Sillybutts/Cynthia/STLs/Black/PlungerRod_Thinner (for tighter springs like k26).stl

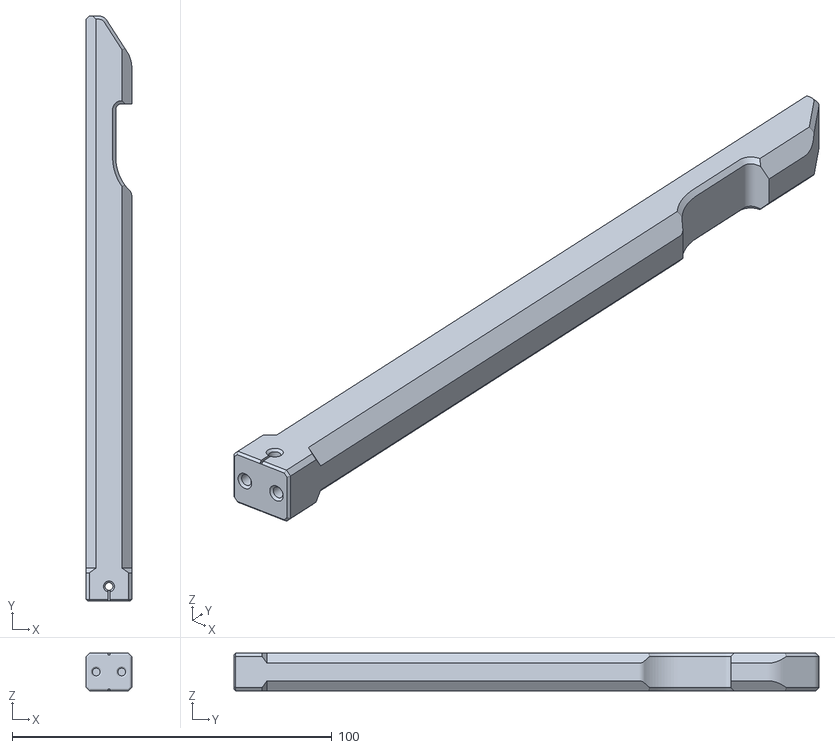
[picture p39: CAD file, 2023-04-10]
STLs/Black/PlungerRod_Thinner (for tighter springs like k26).stl
14.3 x 182.9 x 11.7
