Sillybutts/Cynthia/STLs/Green/Left Handed/MagwellBack_LH_Locked.stl

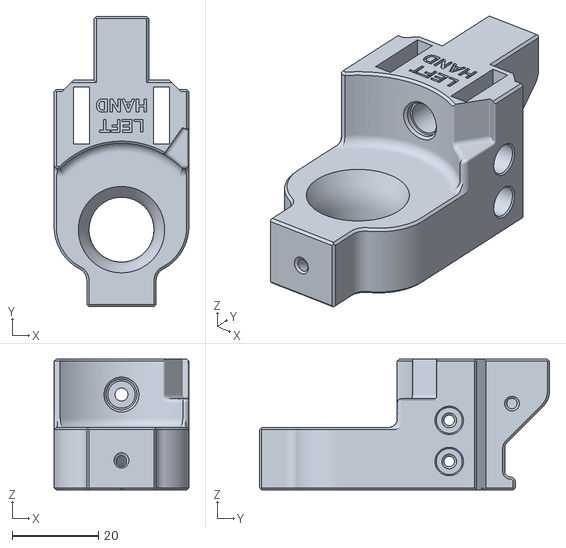
[picture p40: CAD file, 2023-03-23]
STLs/Green/Left Handed/MagwellBack_LH_Locked.stl
31.2 x 67.2 x 30.3
