Sillybutts/Cynthia/STLs/Orange/Trigger_SillyStyle.stl

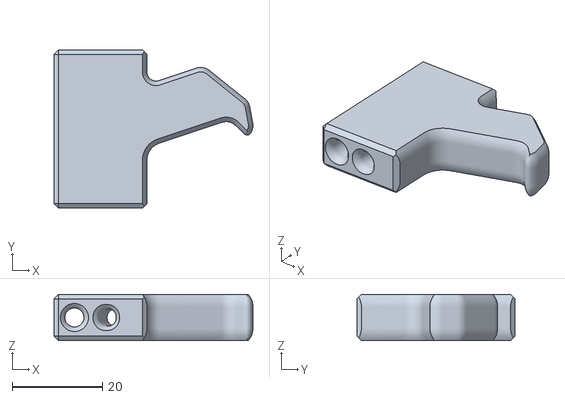
[picture p41: CAD file, 2023-03-23]
STLs/Orange/Trigger_SillyStyle.stl
44.0 x 35.0 x 10.2
