Sillybutts/Cynthia/STLs/Alternate and Experimental/Alternate Mag Release and Trigger Guard/TriggerGuard_LONGERFORALTERNATEMAGRELEASE.stl

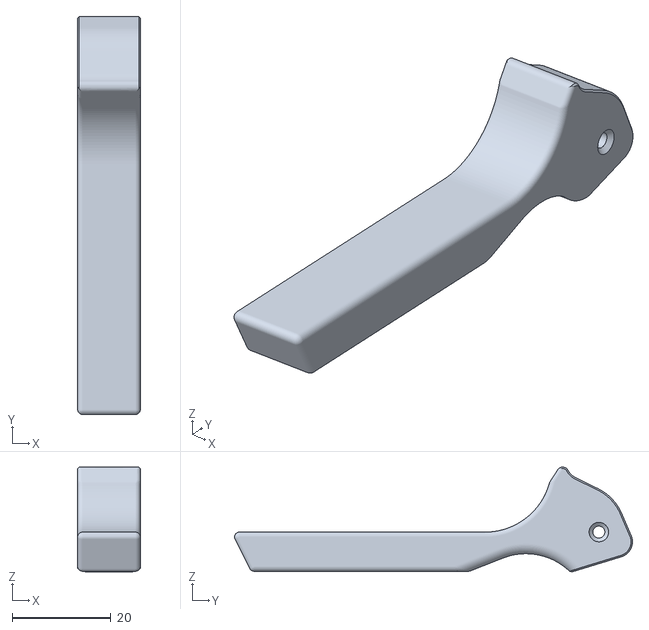
[picture p42: CAD file, 2023-03-24]
STLs/Alternate and Experimental/Alternate Mag Release and Trigger Guard/TriggerGuard_LONGERFORALTERNATEMAGRELEASE.stl
12.7 x 80.5 x 21.2
