Sillybutts/Cynthia/STLs/Alternate and Experimental/Shortened front (needs 5.5inch threaded rod)/SHORTENED_TopRail_SplitA.stl

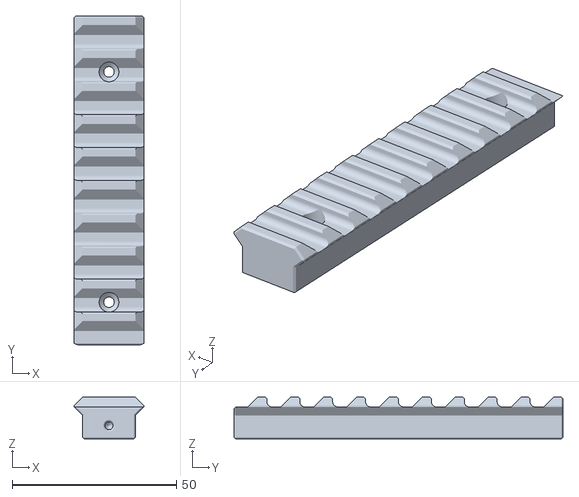
[picture p43: CAD file, 2023-04-16]
STLs/Alternate and Experimental/Shortened front (needs 5.5inch threaded rod)/SHORTENED_TopRail_SplitA.stl
21.2 x 100.1 x 12.7
