Sillybutts/Cynthia/STLs/Alternate and Experimental/Slim front end/SLIM_Muzzle_WithBottomRail.stl

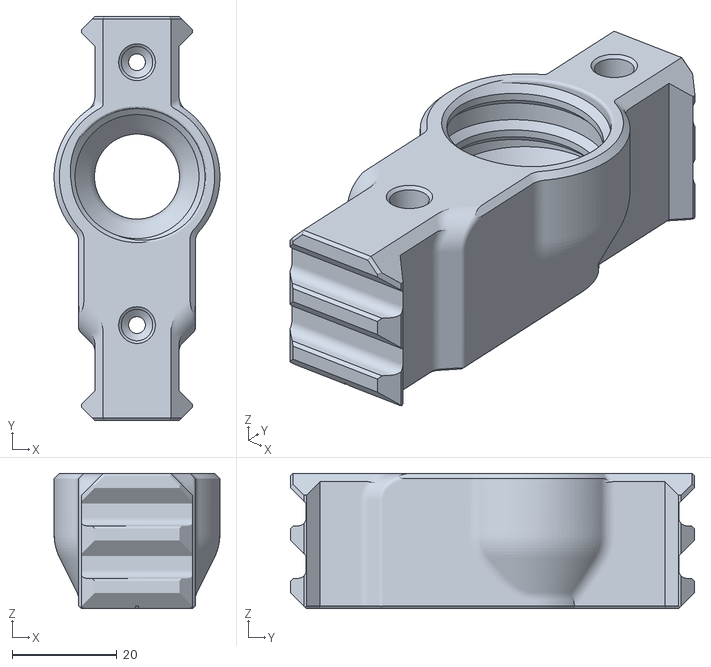
[picture p44: CAD file, 2023-03-23]
STLs/Alternate and Experimental/Slim front end/SLIM_Muzzle_WithBottomRail.stl
31.6 x 77.0 x 25.8
