Sillybutts/Cynthia/STLs/Alternate and Experimental/Split PTcover for smaller printers/SPLIT_PTcoverFront_Logo.stl

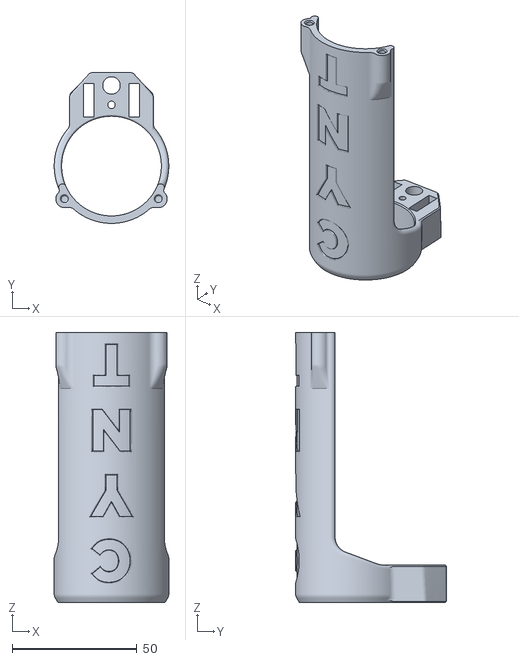
[picture p45: CAD file, 2023-06-04]
STLs/Alternate and Experimental/Split PTcover for smaller printers/SPLIT_PTcoverFront_Logo.stl
46.0 x 60.5 x 108.3
