Sillybutts/Cynthia/STLs/Alternate and Experimental/Stubby front end/DartGuide_Alternate.stl

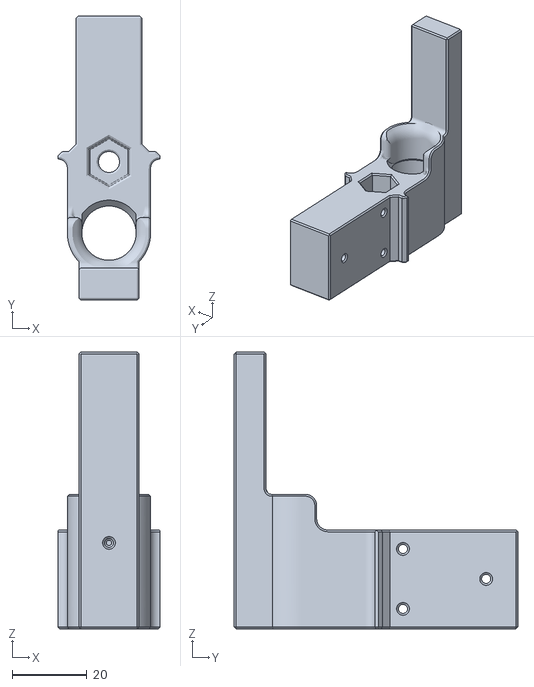
[picture p46: CAD file, 2023-03-23]
STLs/Alternate and Experimental/Stubby front end/DartGuide_Alternate.stl
27.2 x 75.7 x 74.0
