Sillybutts/Cynthia/STLs/Black/Stock_SlingPoints.stl

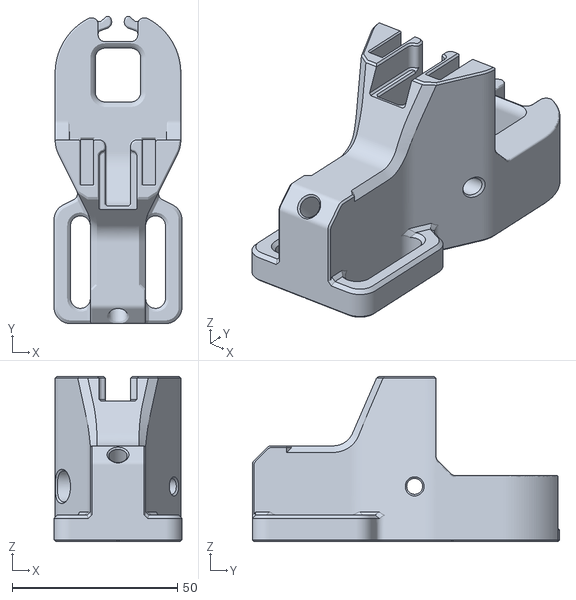
[picture p47: CAD file, 2023-03-23]
STLs/Black/Stock_SlingPoints.stl
38.8 x 93.1 x 50.0
