Sillybutts/Cynthia/STLs/Green/PTcover_Logo.stl

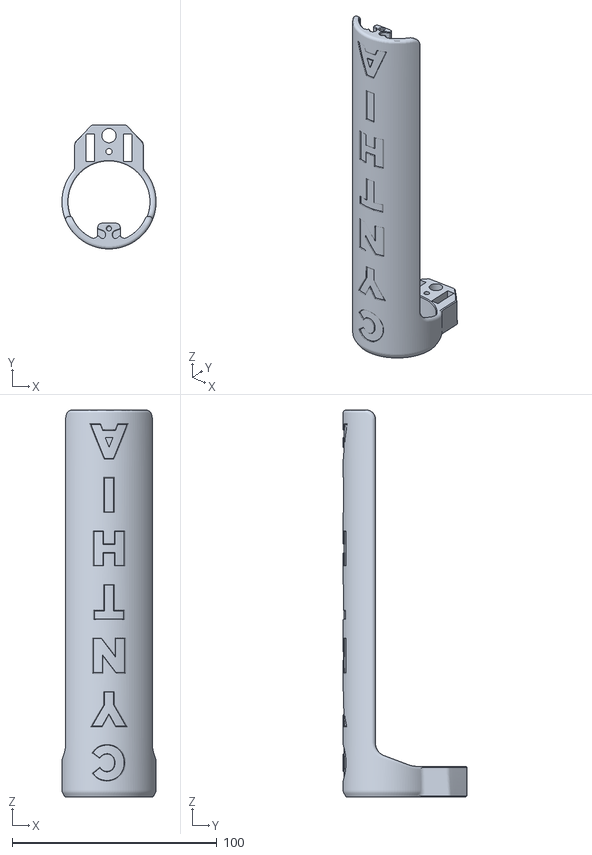
[picture p48: CAD file, 2023-03-27]
STLs/Green/PTcover_Logo.stl
46.0 x 60.5 x 189.1
