Sillybutts/Cynthia/STLs/Orange/Muzzle_WithBottomRail.stl

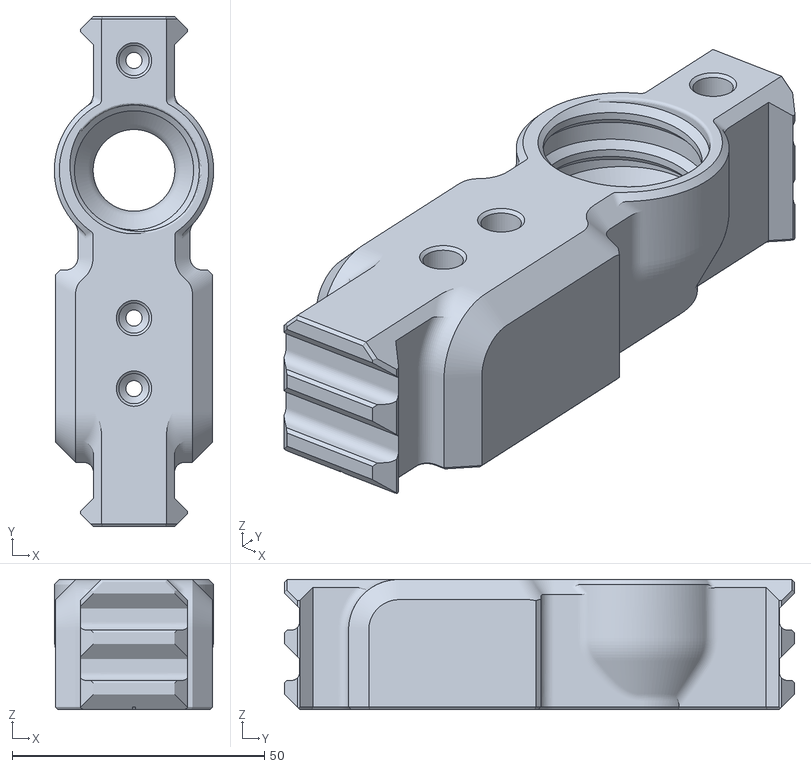
[picture p49: CAD file, 2023-03-23]
STLs/Orange/Muzzle_WithBottomRail.stl
31.6 x 101.2 x 25.8
