Sillybutts/Cynthia/STLs/Alternate and Experimental/MegaXL Spigot SCAR/BarrelCap.stl

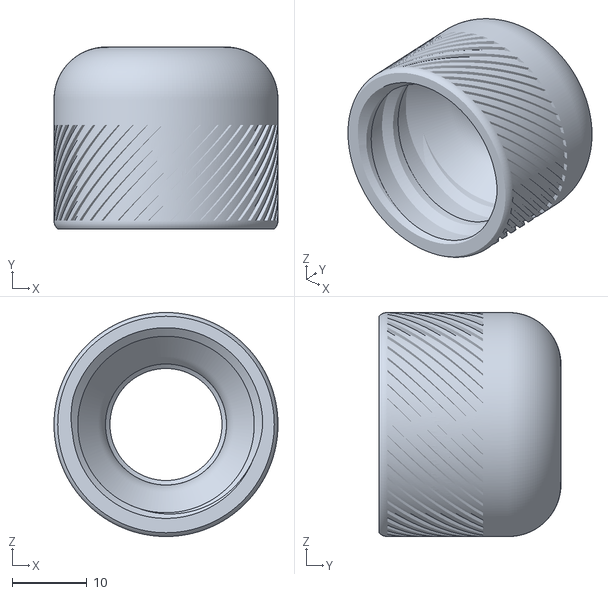
[picture p50: CAD file, 2023-03-23]
STLs/Alternate and Experimental/MegaXL Spigot SCAR/BarrelCap.stl
30.0 x 24.4 x 30.0
