Sillybutts/Cynthia/STLs/Alternate and Experimental/Shortened front (needs 5.5inch threaded rod)/SHORTENED_BottomRail.stl

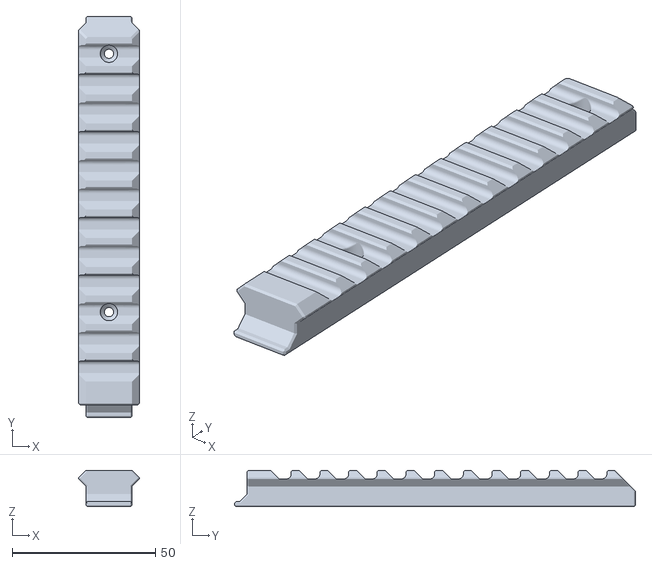
[picture p51: CAD file, 2023-04-16]
STLs/Alternate and Experimental/Shortened front (needs 5.5inch threaded rod)/SHORTENED_BottomRail.stl
21.2 x 139.8 x 12.7
