Sillybutts/Cynthia/STLs/Alternate and Experimental/Stubby front end/MuzzleNut.stl

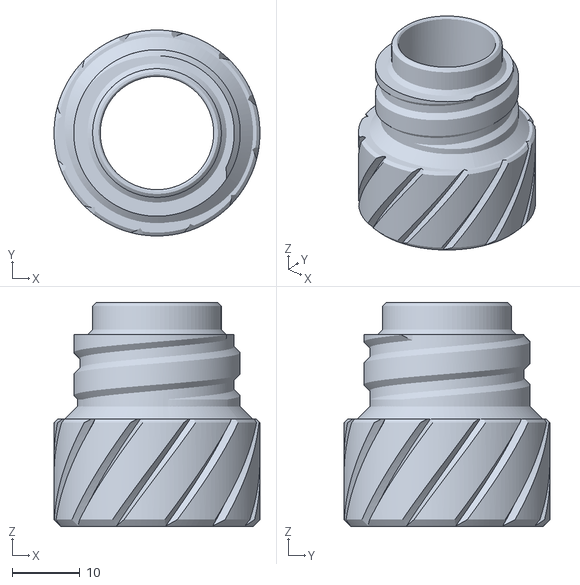
[picture p53: CAD file, 2023-03-23]
STLs/Alternate and Experimental/Stubby front end/MuzzleNut.stl
30.5 x 30.5 x 33.1
