Sillybutts/Cynthia/STLs/Alternate and Experimental/Triggers for optional 10-32 Heat Set Insert/HEATSET_Trigger_ChanceStyle.stl

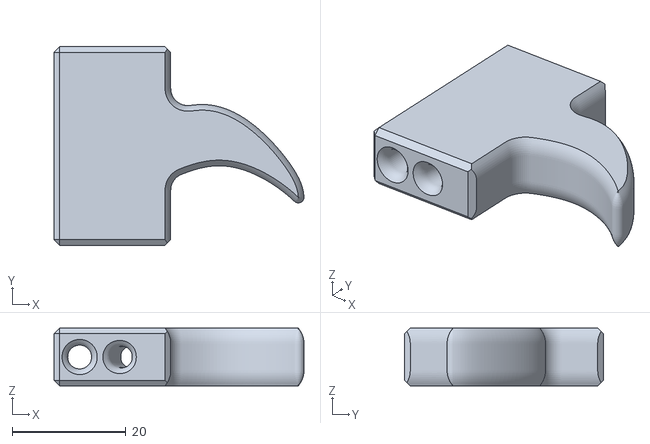
[picture p54: CAD file, 2023-03-23]
STLs/Alternate and Experimental/Triggers for optional 10-32 Heat Set Insert/HEATSET_Trigger_ChanceStyle.stl
44.0 x 35.0 x 10.2
