Sillybutts/Cynthia/STLs/Black/GripBody_NoShoe.stl

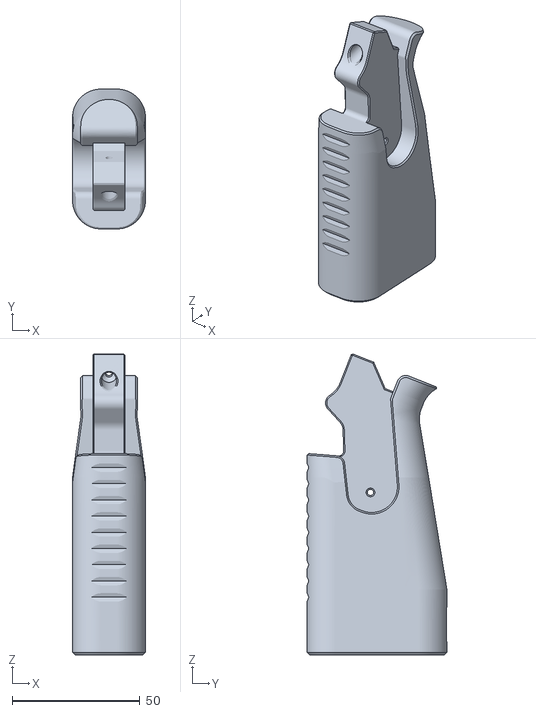
[picture p55: CAD file, 2023-03-23]
STLs/Black/GripBody_NoShoe.stl
28.6 x 54.8 x 117.9
