Sillybutts/Cynthia/STLs/Orange/Catch.stl

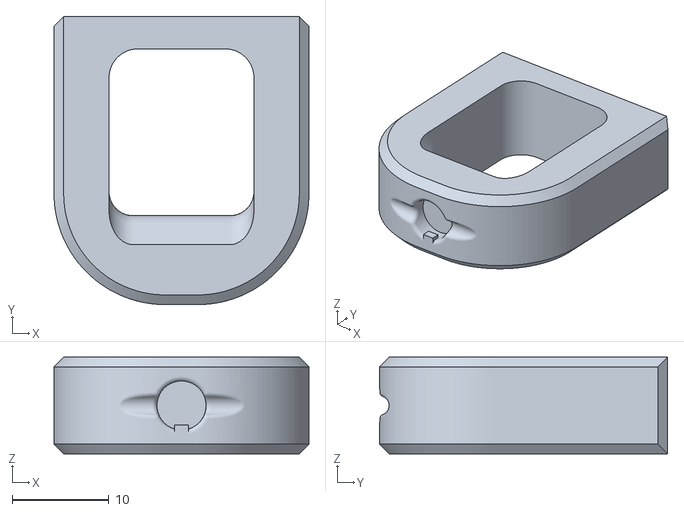
[picture p56: CAD file, 2023-03-23]
STLs/Orange/Catch.stl
26.4 x 29.8 x 10.0
