Sillybutts/Cynthia/STLs/Alternate and Experimental/MegaXL Spigot SCAR/Trivictus MXLspigotSCAR.stl

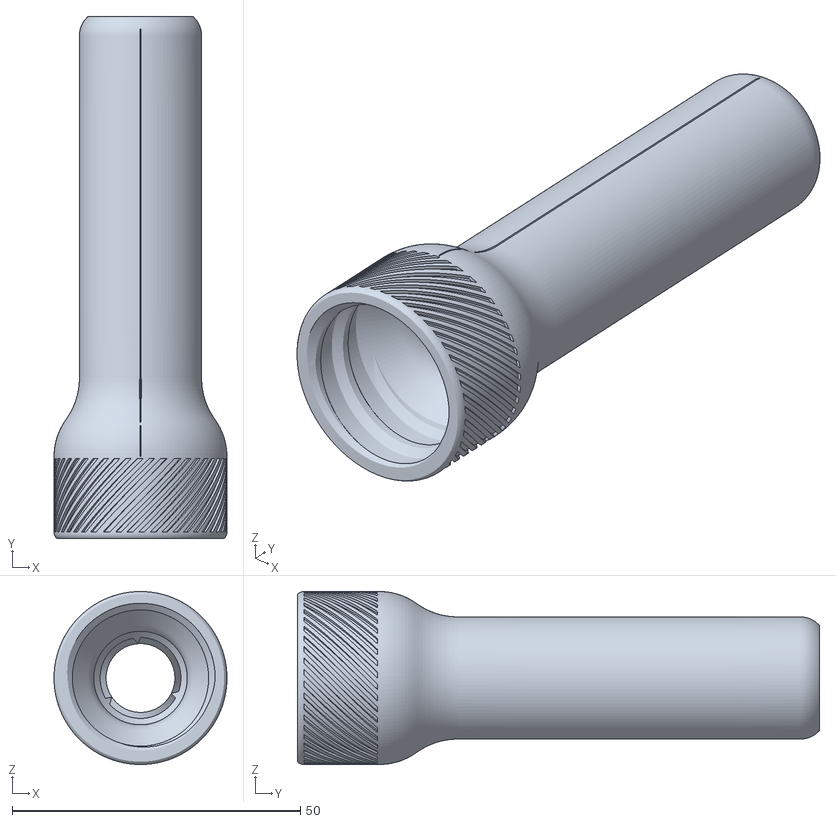
[picture p57: CAD file, 2023-03-23]
STLs/Alternate and Experimental/MegaXL Spigot SCAR/Trivictus MXLspigotSCAR.stl
30.0 x 90.5 x 30.0
