Sillybutts/Cynthia/STLs/Alternate and Experimental/Slim front end/SLIM_Muzzle.stl

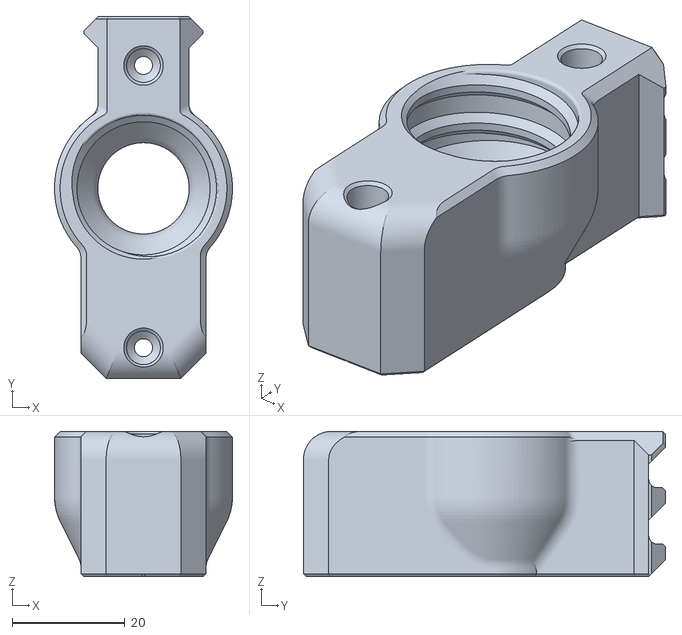
[picture p59: CAD file, 2023-03-23]
STLs/Alternate and Experimental/Slim front end/SLIM_Muzzle.stl
31.6 x 64.3 x 25.8
