Sillybutts/Cynthia/STLs/Alternate and Experimental/Stubby front end/Muzzle.stl

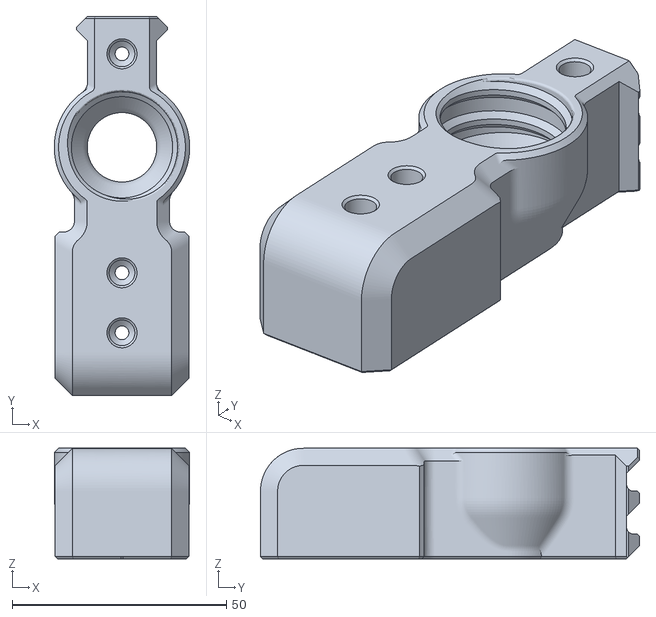
[picture p60: CAD file, 2023-03-23]
STLs/Alternate and Experimental/Stubby front end/Muzzle.stl
31.6 x 88.4 x 25.8
