Sillybutts/Cynthia/STLs/Alternate and Experimental/Triggers for optional 10-32 Heat Set Insert/HEATSET_Trigger_Thicker_SillyStyle.stl

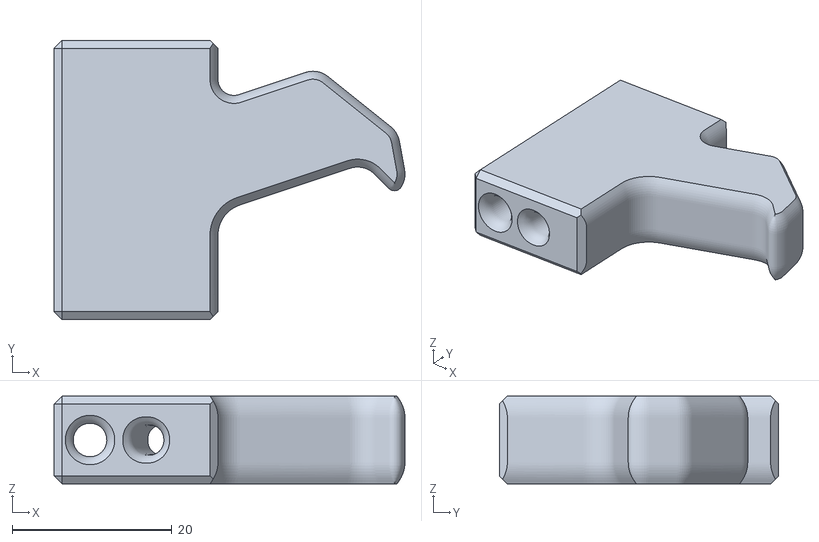
[picture p61: CAD file, 2023-03-23]
STLs/Alternate and Experimental/Triggers for optional 10-32 Heat Set Insert/HEATSET_Trigger_Thicker_SillyStyle.stl
44.0 x 35.0 x 11.0
