Sillybutts/Cynthia/STLs/Black/Buttplate_LongX1.stl

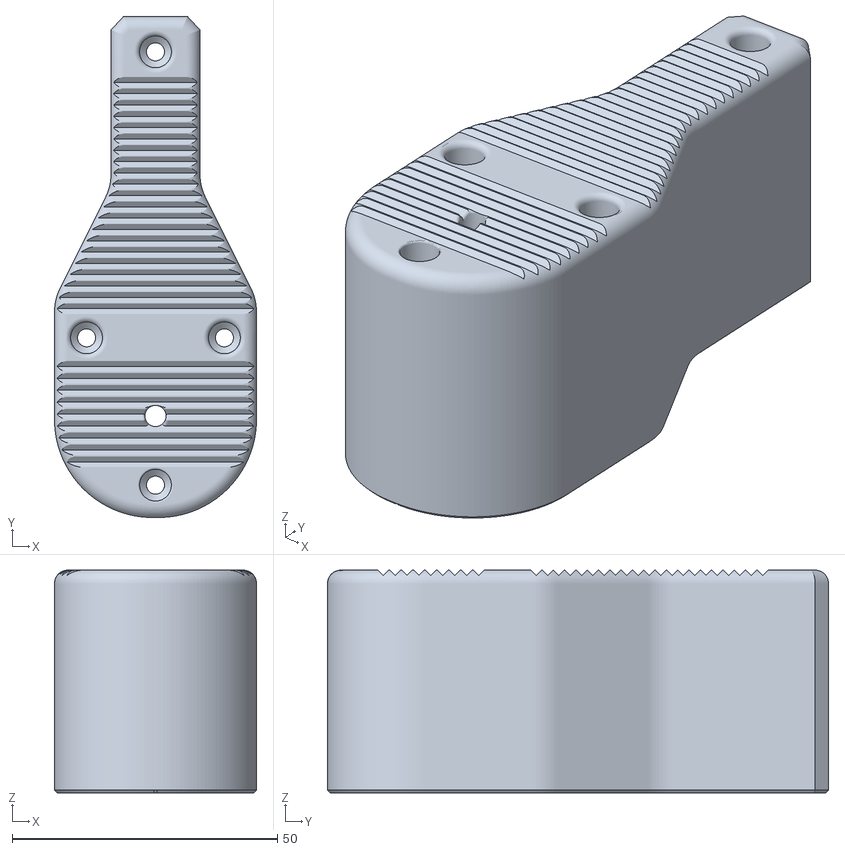
[picture p62: CAD file, 2023-03-23]
STLs/Black/Buttplate_LongX1.stl
38.1 x 94.5 x 42.0
