Sillybutts/Cynthia/STLs/Orange/Trigger_Thicker_ChanceStyle.stl

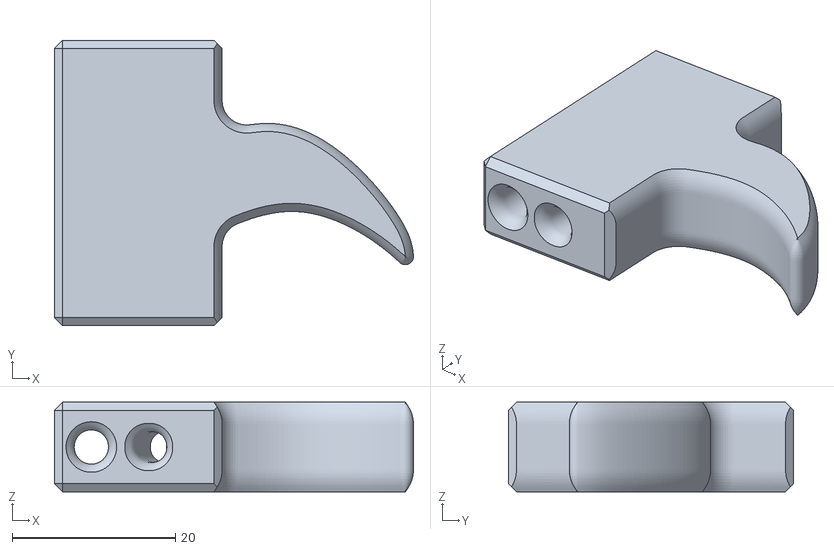
[picture p63: CAD file, 2023-03-23]
STLs/Orange/Trigger_Thicker_ChanceStyle.stl
44.0 x 35.0 x 11.0
