Sillybutts/Cynthia/STLs/Alternate and Experimental/Slim front end/SLIM_FrontBlock_Ported_Blank_SideRails.stl

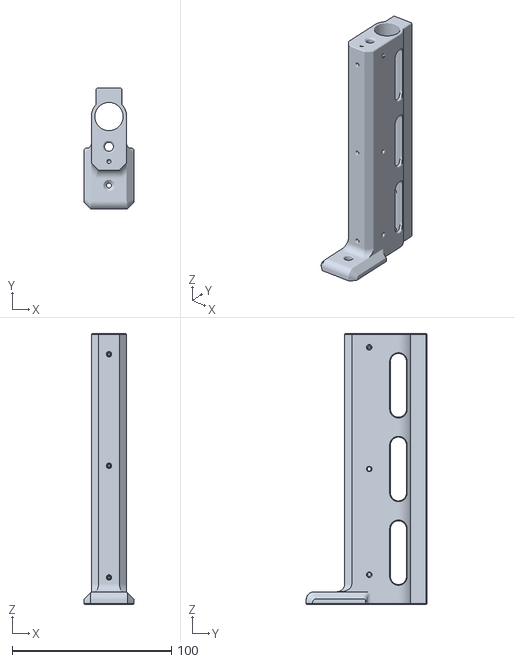
[picture p65: CAD file, 2023-03-23]
STLs/Alternate and Experimental/Slim front end/SLIM_FrontBlock_Ported_Blank_SideRails.stl
31.2 x 75.7 x 170.1
