Sillybutts/Cynthia/STLs/Black/PlungerCap_PreTextured.stl

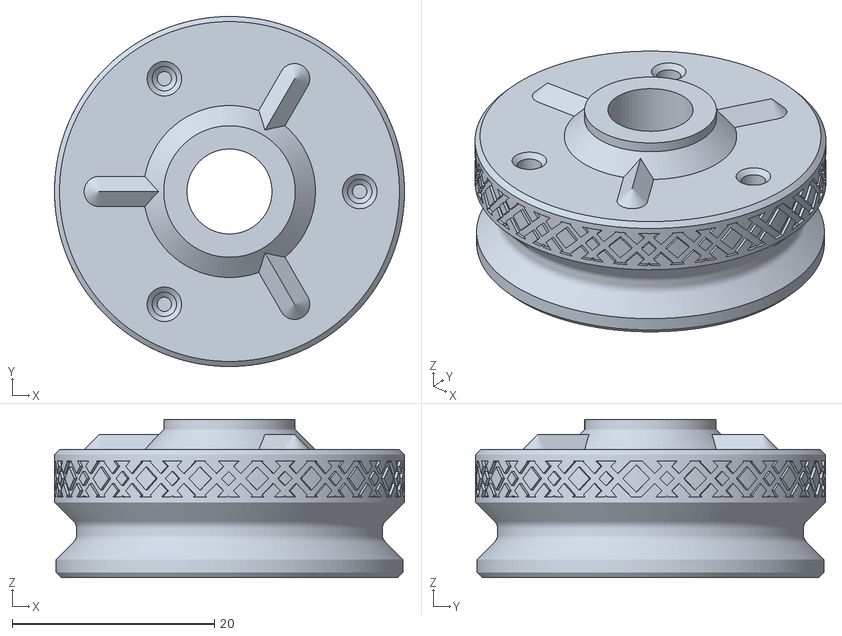
[picture p66: CAD file, 2023-03-23]
STLs/Black/PlungerCap_PreTextured.stl
34.6 x 34.6 x 15.7
