Sillybutts/Cynthia/STLs/Green/FrontBlock_Blank_SideRails.stl

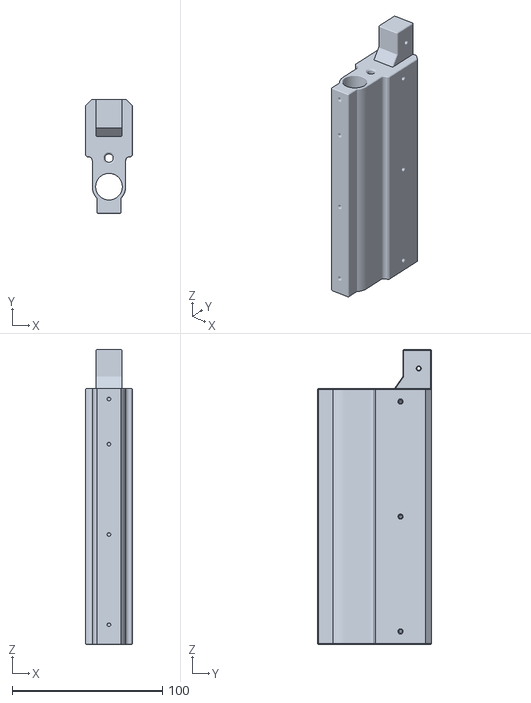
[picture p67: CAD file, 2023-03-23]
STLs/Green/FrontBlock_Blank_SideRails.stl
31.2 x 75.7 x 196.1
