Sillybutts/Cynthia/STLs/Orange/CatchPusher.stl

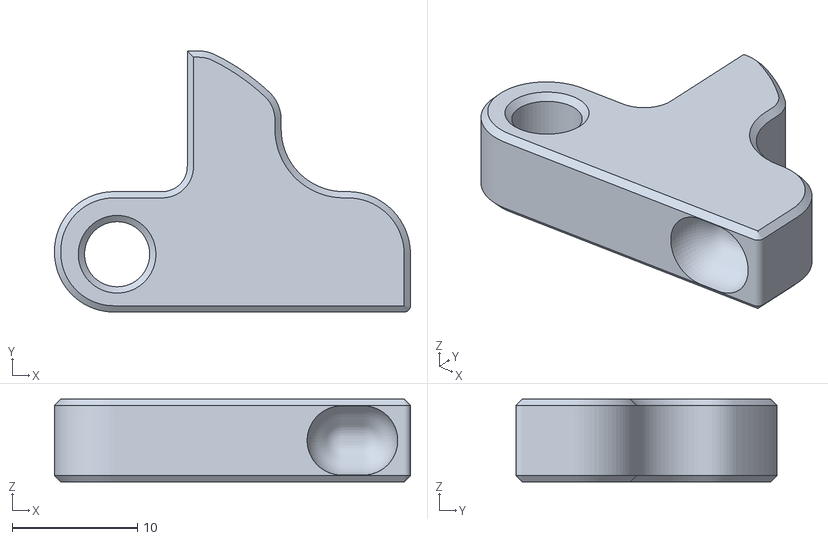
[picture p68: CAD file, 2023-03-23]
STLs/Orange/CatchPusher.stl
28.4 x 20.8 x 6.60
