Sillybutts/Cynthia/STLs/Alternate and Experimental/Shortened front (needs 5.5inch threaded rod)/SHORTENED_FrontBlock_Named.stl

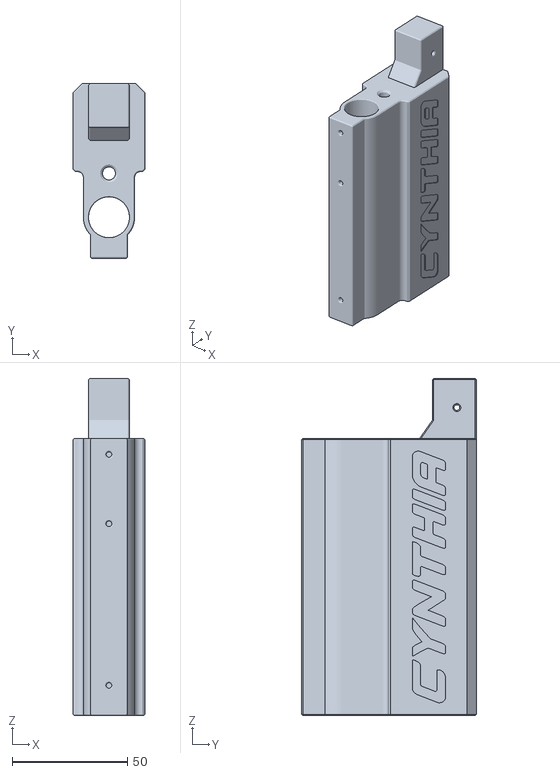
[picture p69: CAD file, 2023-04-16]
STLs/Alternate and Experimental/Shortened front (needs 5.5inch threaded rod)/SHORTENED_FrontBlock_Named.stl
31.2 x 75.7 x 146.1
