Sillybutts/Cynthia/STLs/Black/TopRail_SplitA_NoRail.stl

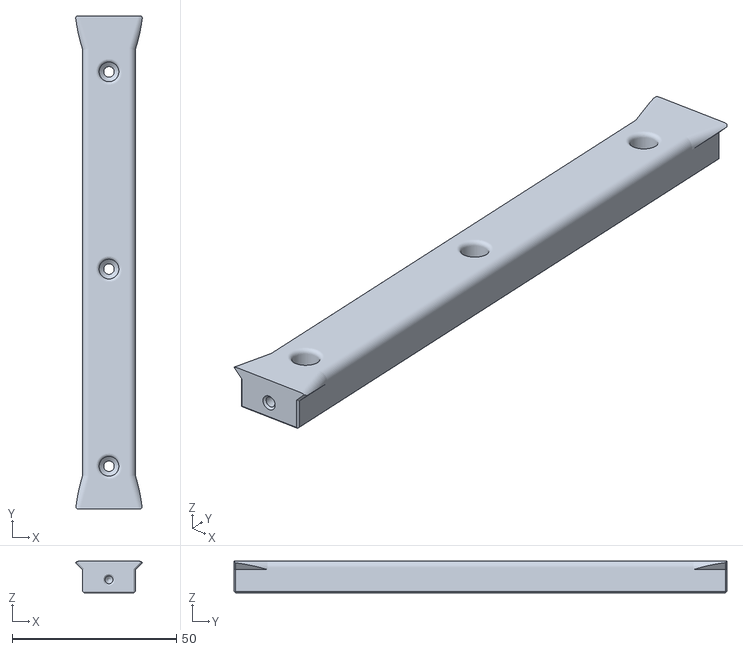
[picture p70: CAD file, 2023-03-23]
STLs/Black/TopRail_SplitA_NoRail.stl
20.3 x 150.1 x 9.72
