Sillybutts/Cynthia/STLs/Green/optional body spacer 1mm.stl

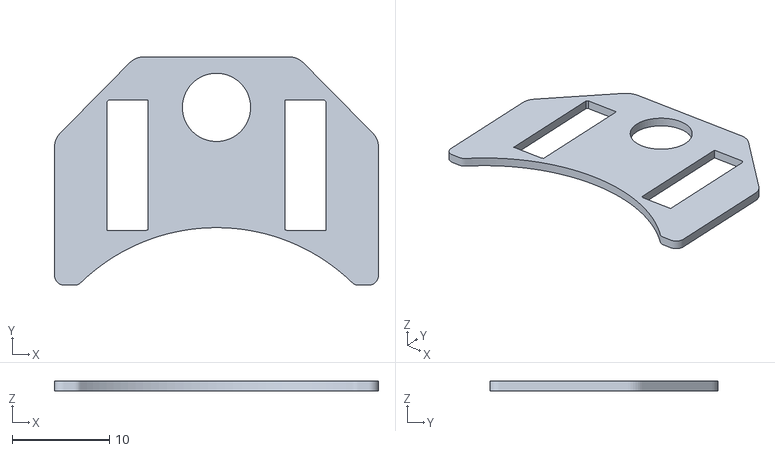
[picture p71: CAD file, 2023-03-23]
STLs/Green/optional body spacer 1mm.stl
33.2 x 23.4 x 1.00
