Sillybutts/Cynthia/STLs/Orange/Trigger_ChanceStyle.stl

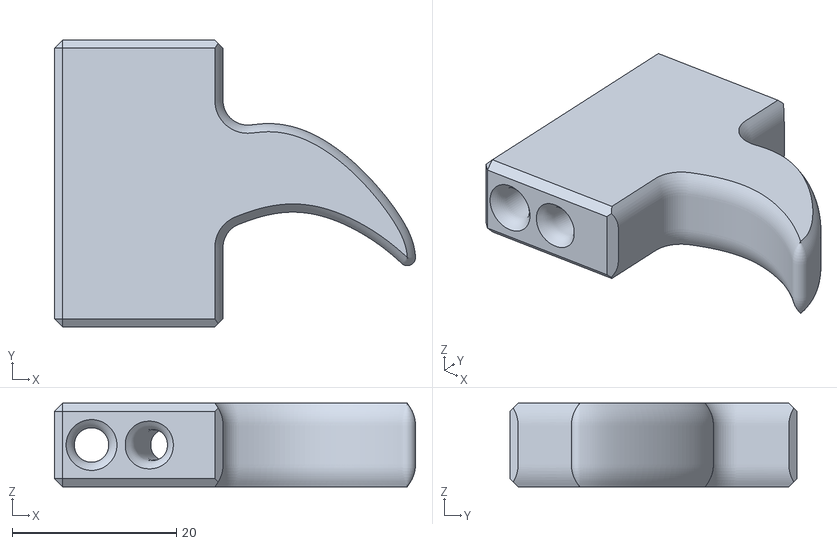
[picture p72: CAD file, 2023-03-23]
STLs/Orange/Trigger_ChanceStyle.stl
44.0 x 35.0 x 10.2
