Sillybutts/Cynthia/STLs/Black/GripBody_WithShoe.stl

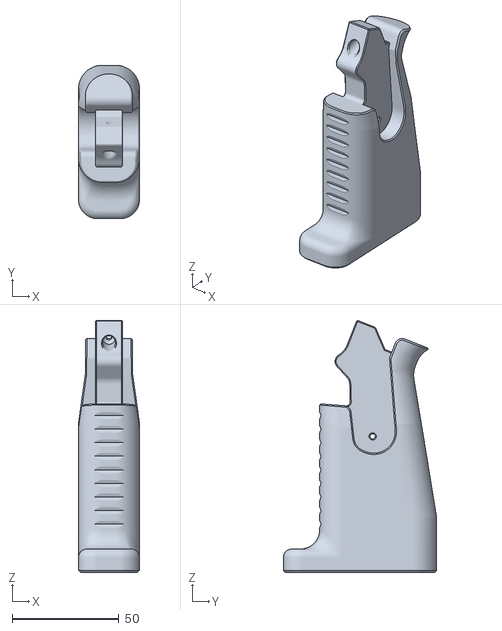
[picture p73: CAD file, 2023-03-23]
STLs/Black/GripBody_WithShoe.stl
28.6 x 71.8 x 117.9
