Sillybutts/Cynthia/STLs/Green/FrontBlock_Ported_Blank_SideRails.stl

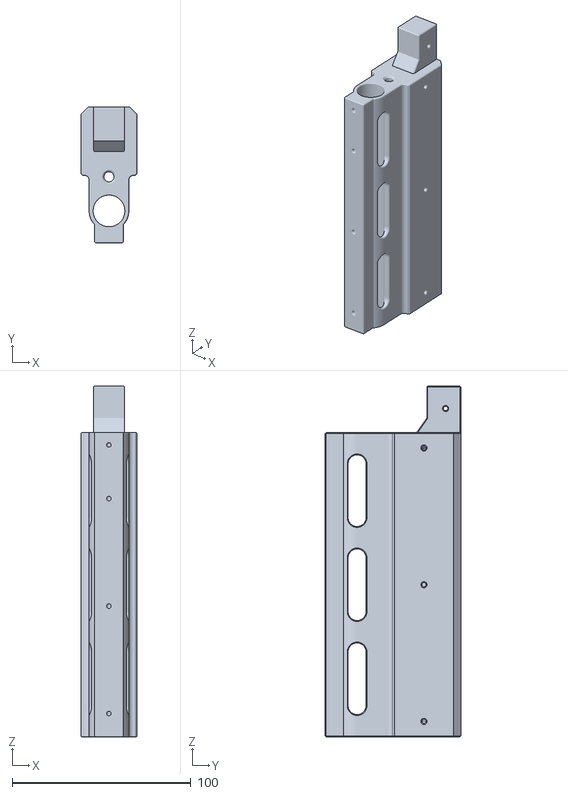
[picture p74: CAD file, 2023-03-23]
STLs/Green/FrontBlock_Ported_Blank_SideRails.stl
31.2 x 75.7 x 196.1
