Sillybutts/Cynthia/STLs/Orange/MagRelease.stl

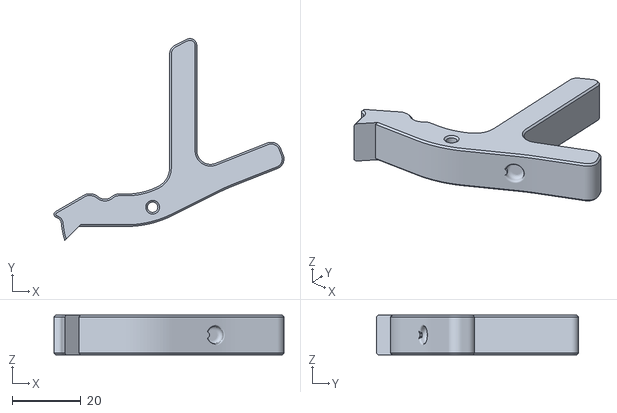
[picture p75: CAD file, 2023-03-23]
STLs/Orange/MagRelease.stl
67.0 x 58.8 x 11.5
