Sillybutts/Cynthia/STLs/Black/TopRail_SplitA.stl

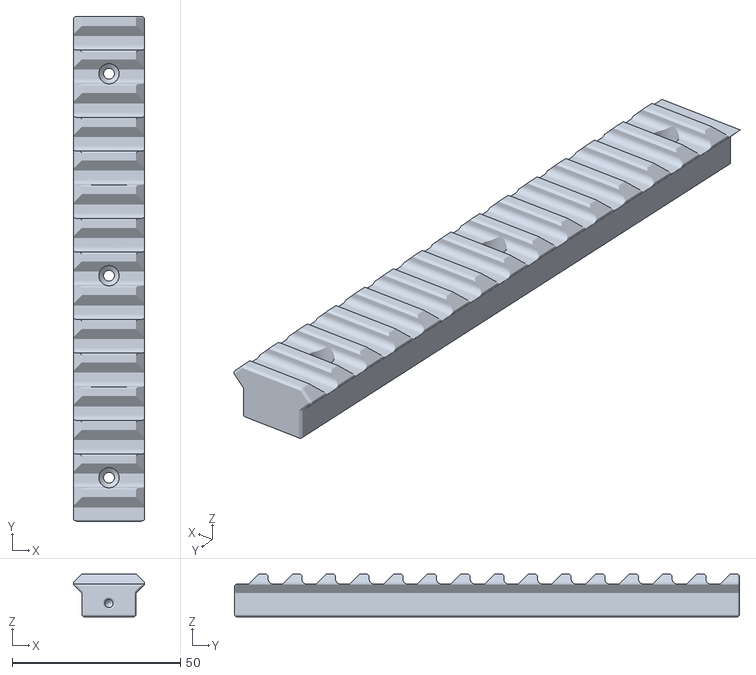
[picture p76: CAD file, 2023-03-23]
STLs/Black/TopRail_SplitA.stl
21.2 x 150.1 x 12.7
