Sillybutts/Cynthia/STLs/Green/BackBlock.stl

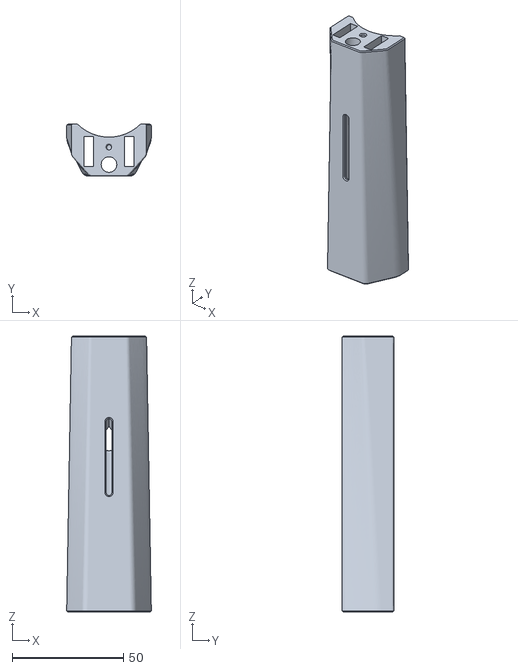
[picture p77: CAD file, 2023-03-23]
STLs/Green/BackBlock.stl
38.1 x 23.4 x 124.1
