Sillybutts/Cynthia/STLs/Orange/PlungerHead.stl

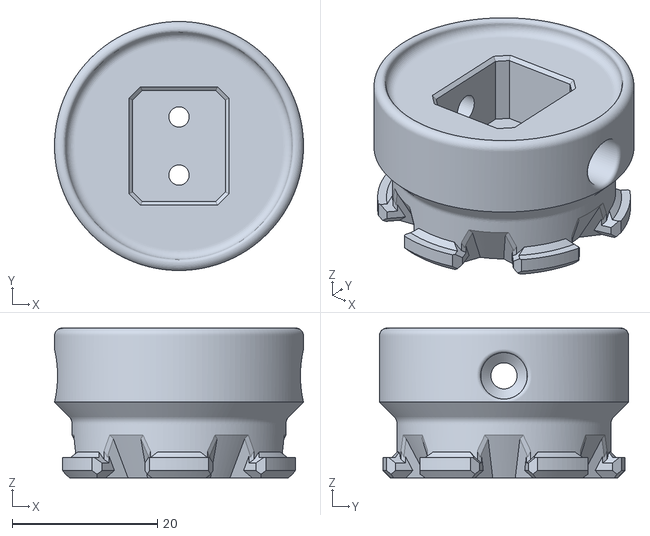
[picture p78: CAD file, 2023-03-23]
STLs/Orange/PlungerHead.stl
34.3 x 34.3 x 20.6
