Sillybutts/Cynthia/STLs/Black/PlungerCap_Plain.stl

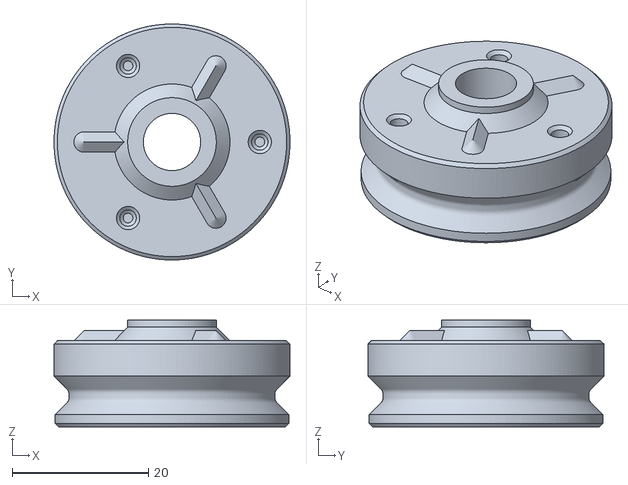
[picture p79: CAD file, 2023-03-23]
STLs/Black/PlungerCap_Plain.stl
34.6 x 34.6 x 15.7
