Sillybutts/Cynthia/STLs/Orange/FrontGripKeeper.stl

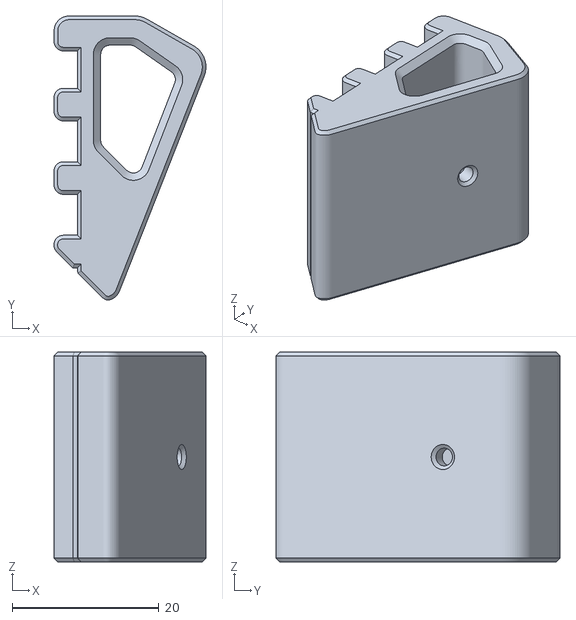
[picture p80: CAD file, 2023-03-23]
STLs/Orange/FrontGripKeeper.stl
20.7 x 38.7 x 28.6
