Sillybutts/Cynthia/STLs/Black/BottomRail_NoAngleFront(For use with Muzzle_WithBottomRail).stl

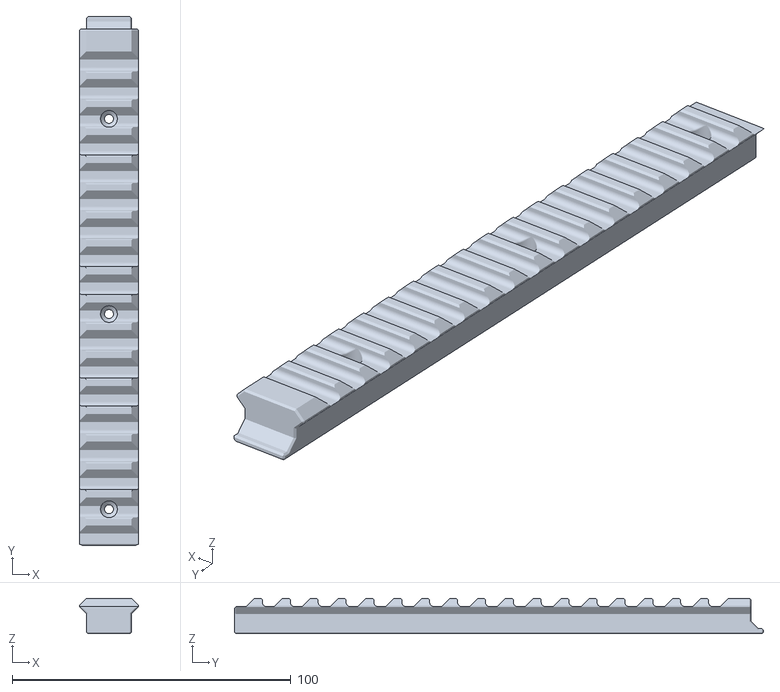
[picture p81: CAD file, 2023-03-23]
STLs/Black/BottomRail_NoAngleFront(For use with Muzzle_WithBottomRail).stl
21.2 x 189.9 x 12.7
