Sillybutts/Cynthia/STLs/Green/DartGuide.stl

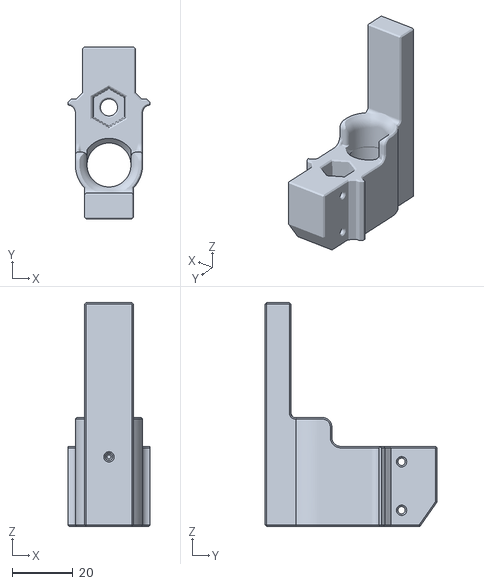
[picture p82: CAD file, 2023-03-23]
STLs/Green/DartGuide.stl
27.2 x 56.7 x 74.0
