Sillybutts/Cynthia/STLs/Green/optional body spacer 2mm.stl

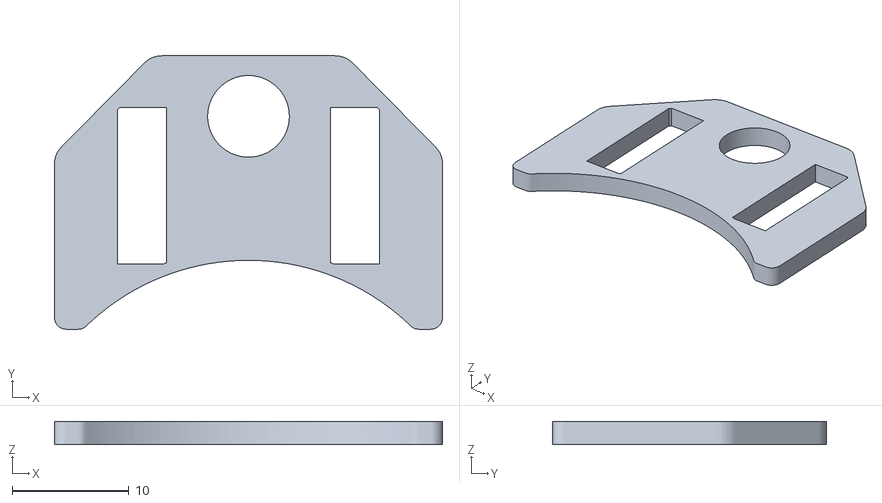
[picture p83: CAD file, 2023-03-23]
STLs/Green/optional body spacer 2mm.stl
33.2 x 23.4 x 2.00
