Sillybutts/Cynthia/STLs/Alternate and Experimental/Slim front end/SLIM_FrontBlock_Ported_Blank.stl

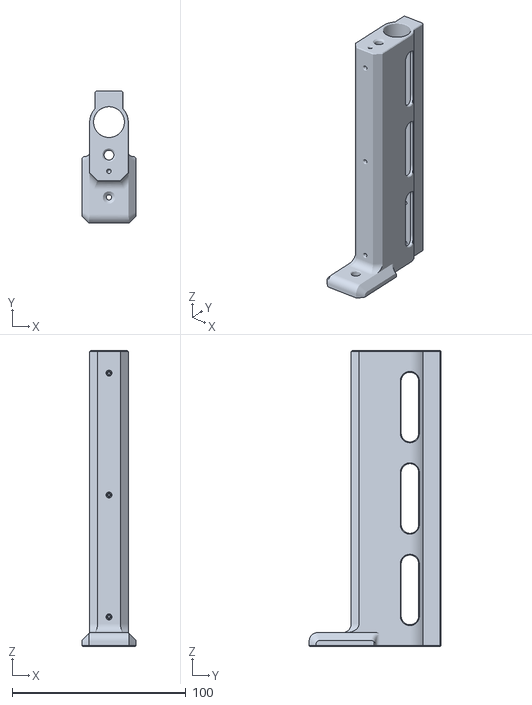
[picture p84: CAD file, 2023-03-23]
STLs/Alternate and Experimental/Slim front end/SLIM_FrontBlock_Ported_Blank.stl
31.2 x 75.7 x 170.1
