Sillybutts/Cynthia/STLs/Black/PTguideBase.stl

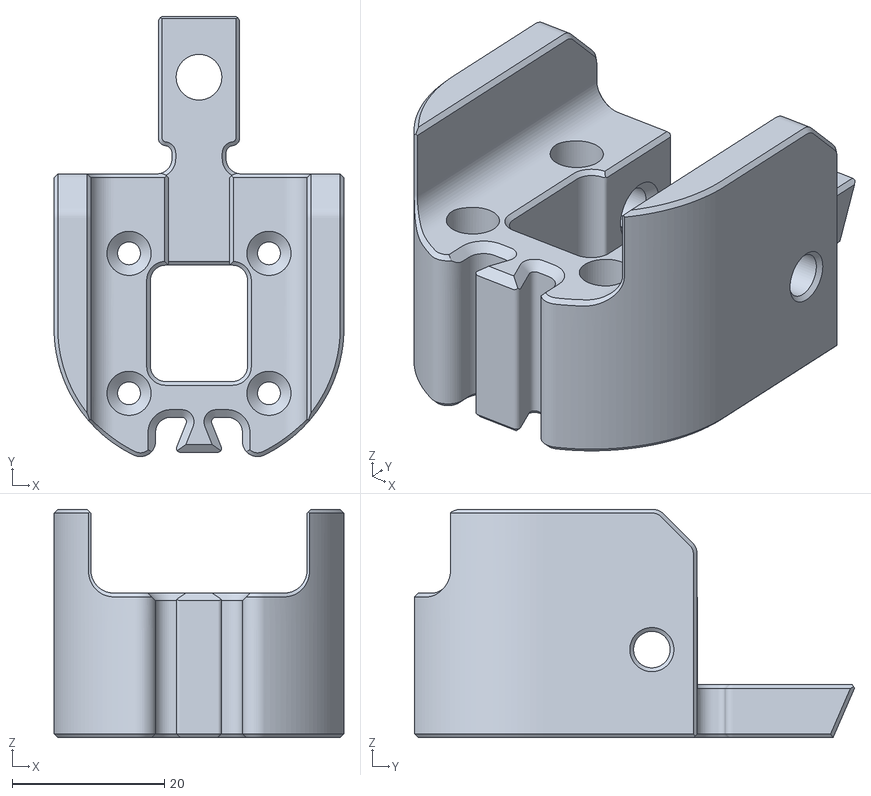
[picture p85: CAD file, 2023-03-23]
STLs/Black/PTguideBase.stl
38.1 x 57.8 x 30.0
