Sillybutts/Cynthia/STLs/Green/MidBlock.stl

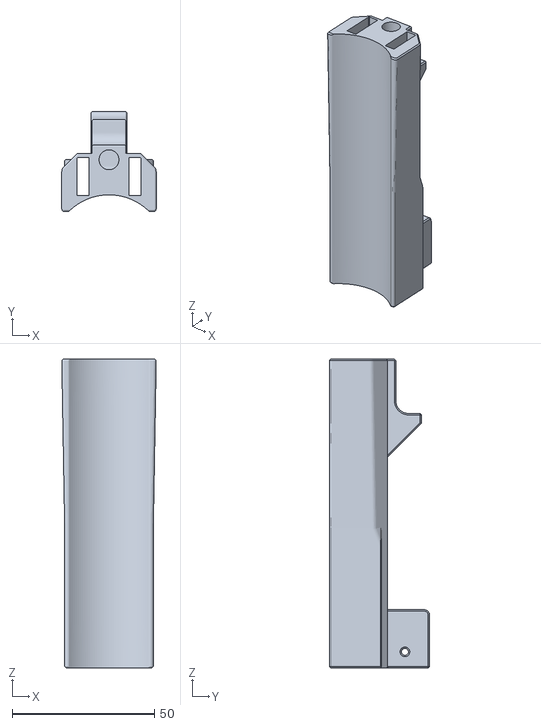
[picture p86: CAD file, 2023-03-23]
STLs/Green/MidBlock.stl
33.2 x 35.3 x 108.7
