Sillybutts/Cynthia/STLs/Black/PlungerRod.stl

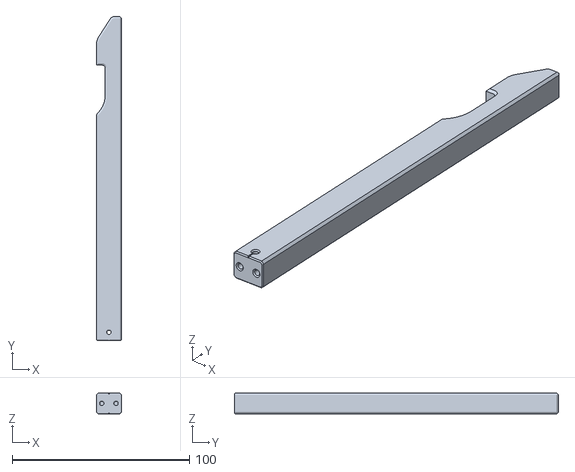
[picture p87: CAD file, 2023-03-23]
STLs/Black/PlungerRod.stl
14.3 x 182.9 x 11.7
