Sillybutts/Cynthia/STLs/Green/Grip_R.stl

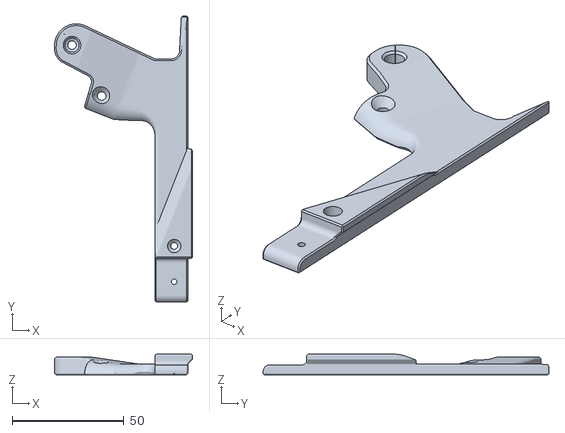
[picture p88: CAD file, 2023-03-23]
STLs/Green/Grip_R.stl
61.8 x 128.0 x 9.25
