Sillybutts/Cynthia/STLs/Black/ThumbholeStock.stl

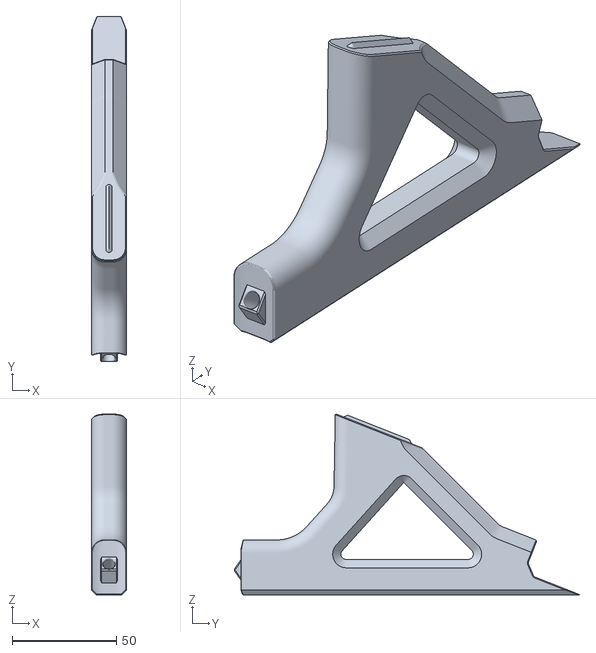
[picture p89: CAD file, 2023-03-23]
STLs/Black/ThumbholeStock.stl
16.8 x 165.7 x 86.9
