Sillybutts/Cynthia/STLs/Green/PTguide.stl

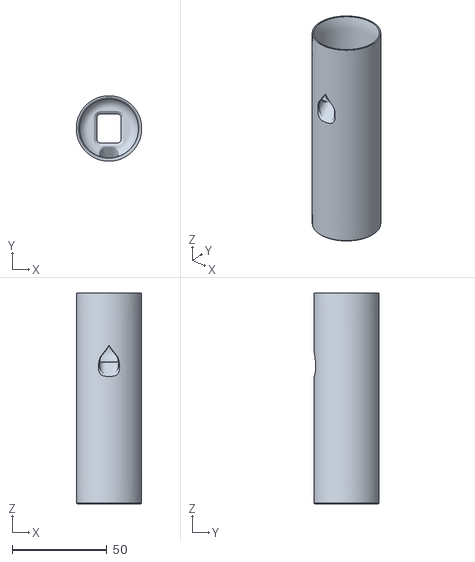
[picture p90: CAD file, 2023-03-23]
STLs/Green/PTguide.stl
34.6 x 34.6 x 111.5
