Sillybutts/Cynthia/STLs/Black/MagwellChin.stl

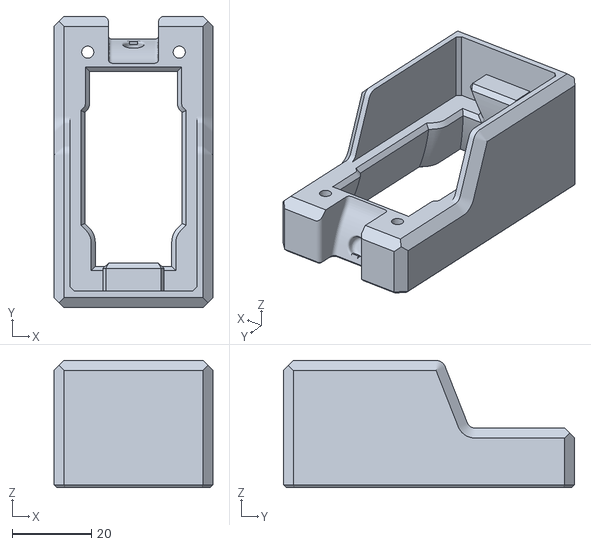
[picture p91: CAD file, 2023-03-23]
STLs/Black/MagwellChin.stl
40.1 x 73.4 x 32.0
