Sillybutts/Cynthia/STLs/Black/Buttplate_Short.stl

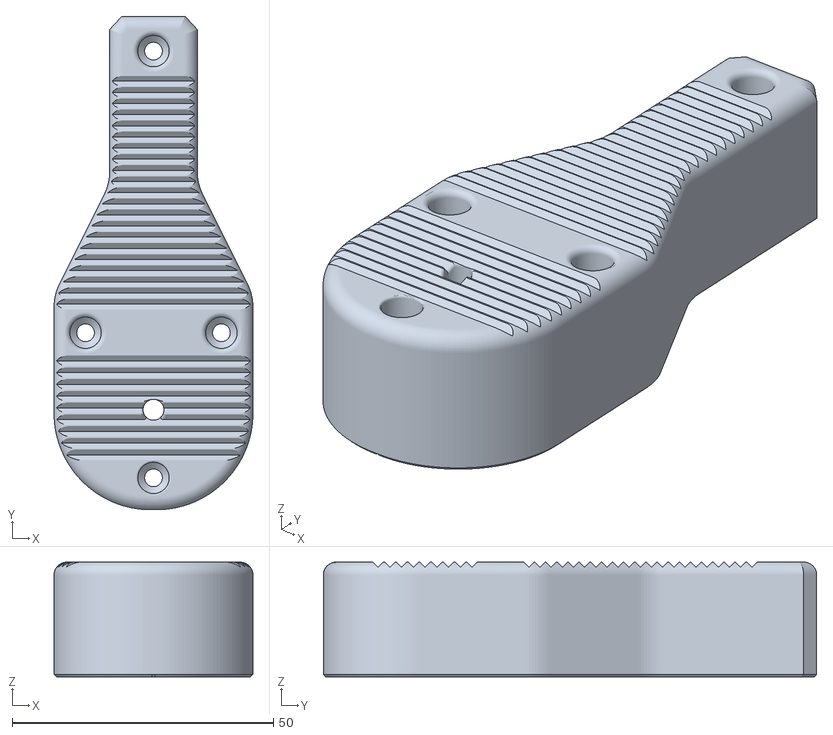
[picture p93: CAD file, 2023-03-23]
STLs/Black/Buttplate_Short.stl
38.1 x 94.5 x 22.0
