Sillybutts/Cynthia/STLs/Black/TopRail_SplitB.stl

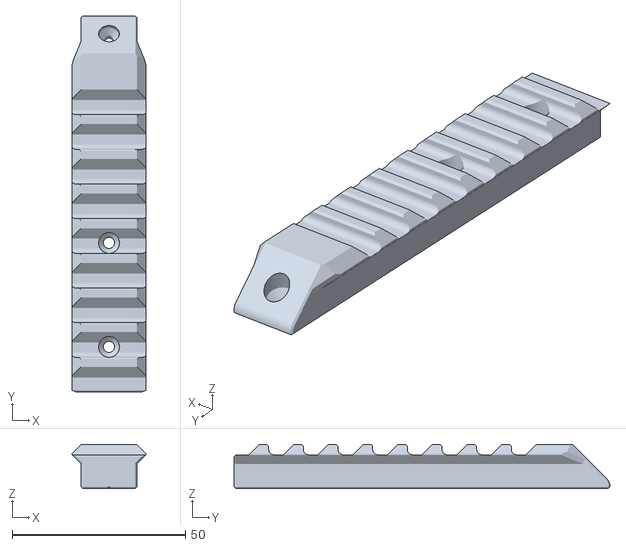
[picture p94: CAD file, 2023-03-23]
STLs/Black/TopRail_SplitB.stl
21.2 x 108.5 x 12.7
