Sillybutts/Cynthia/STLs/Black/FrontGrip_YesBackstop.stl

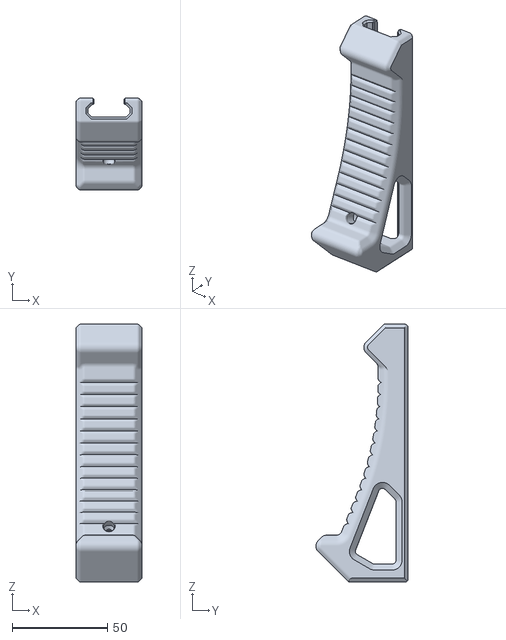
[picture p96: CAD file, 2023-03-23]
STLs/Black/FrontGrip_YesBackstop.stl
34.9 x 48.6 x 135.7
