Sillybutts/Cynthia/STLs/Black/Buttplate_LongX3.stl

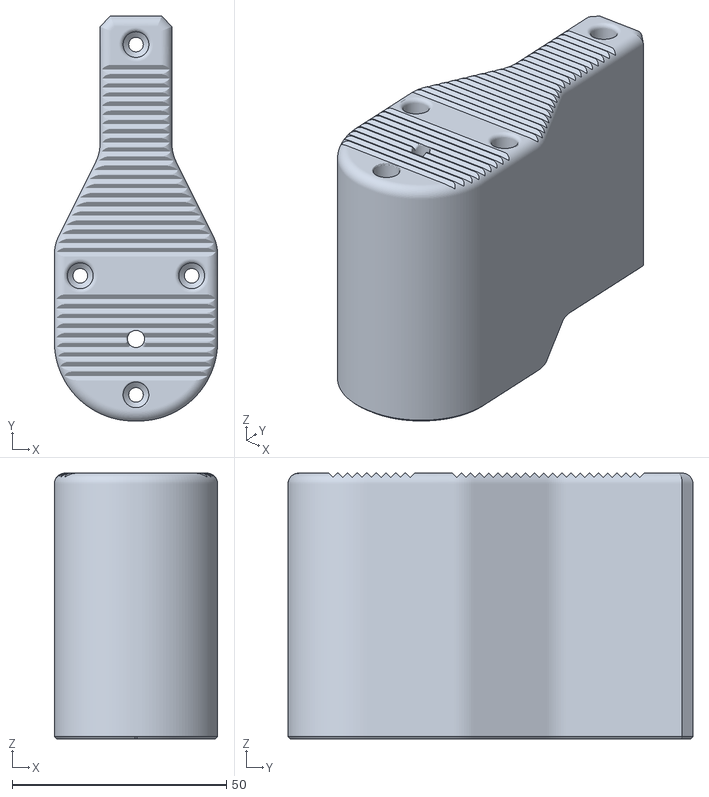
[picture p97: CAD file, 2023-03-23]
STLs/Black/Buttplate_LongX3.stl
38.1 x 94.5 x 62.0
