Sillybutts/Cynthia/STLs/Black/SideRail_SIDERAILFRONTBLOCKONLY.stl

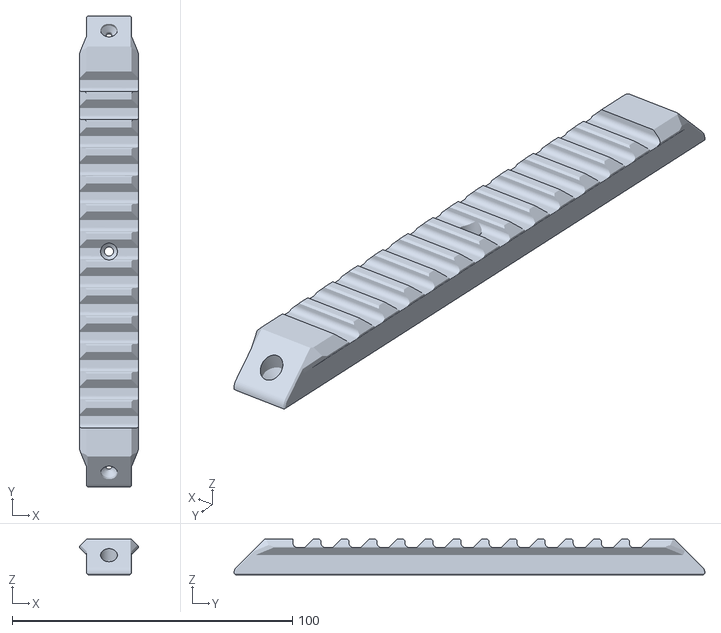
[picture p98: CAD file, 2023-03-23]
STLs/Black/SideRail_SIDERAILFRONTBLOCKONLY.stl
21.2 x 168.1 x 12.7
