Sillybutts/Cynthia/STLs/Black/TriggerGuard.stl

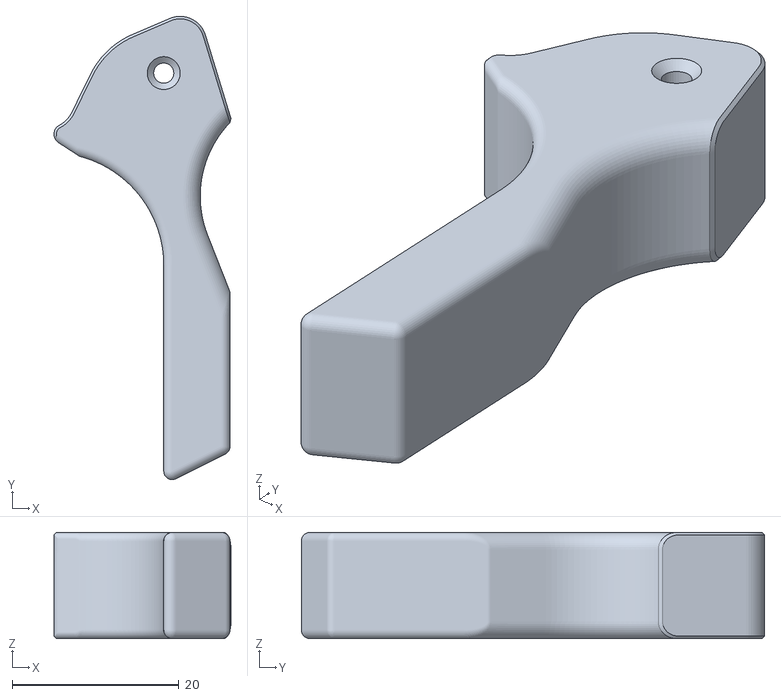
[picture p99: CAD file, 2023-03-23]
STLs/Black/TriggerGuard.stl
21.2 x 55.5 x 12.7
