Sillybutts/Cynthia/STLs/Black/FrontGrip_NoBackstop.stl

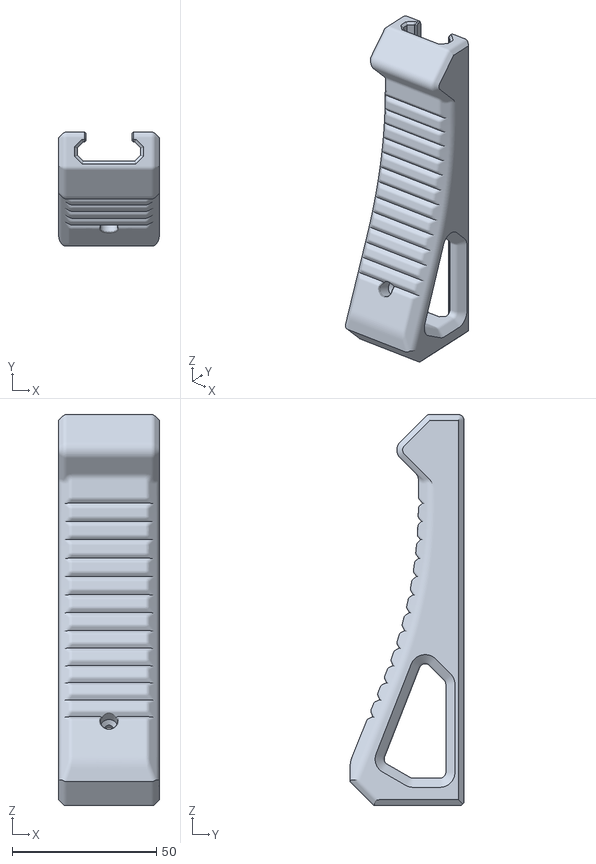
[picture p100: CAD file, 2023-03-23]
STLs/Black/FrontGrip_NoBackstop.stl
34.9 x 39.6 x 135.7
