Sillybutts/Cynthia/STLs/Black/Stock.stl

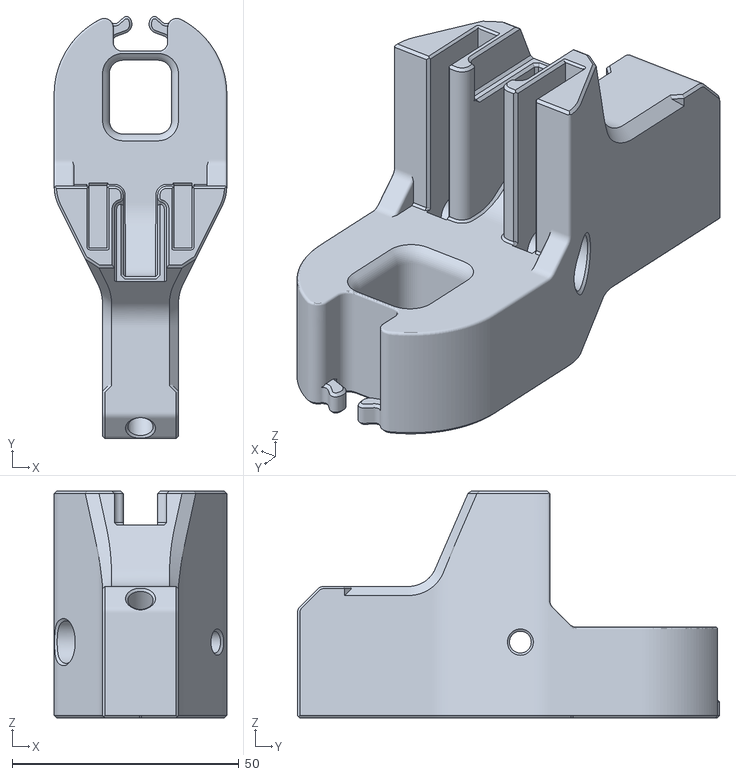
[picture p101: CAD file, 2023-03-23]
STLs/Black/Stock.stl
38.1 x 93.1 x 50.0
