Sillybutts/Cynthia/STLs/Black/Buttplate_LongX2.stl

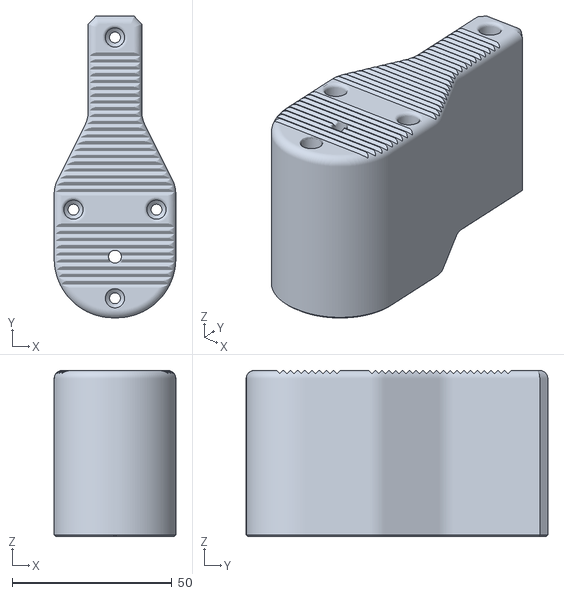
[picture p102: CAD file, 2023-03-23]
STLs/Black/Buttplate_LongX2.stl
38.1 x 94.5 x 52.0
