Sillybutts/Cynthia/STLs/Black/BottomRail_NoRail.stl

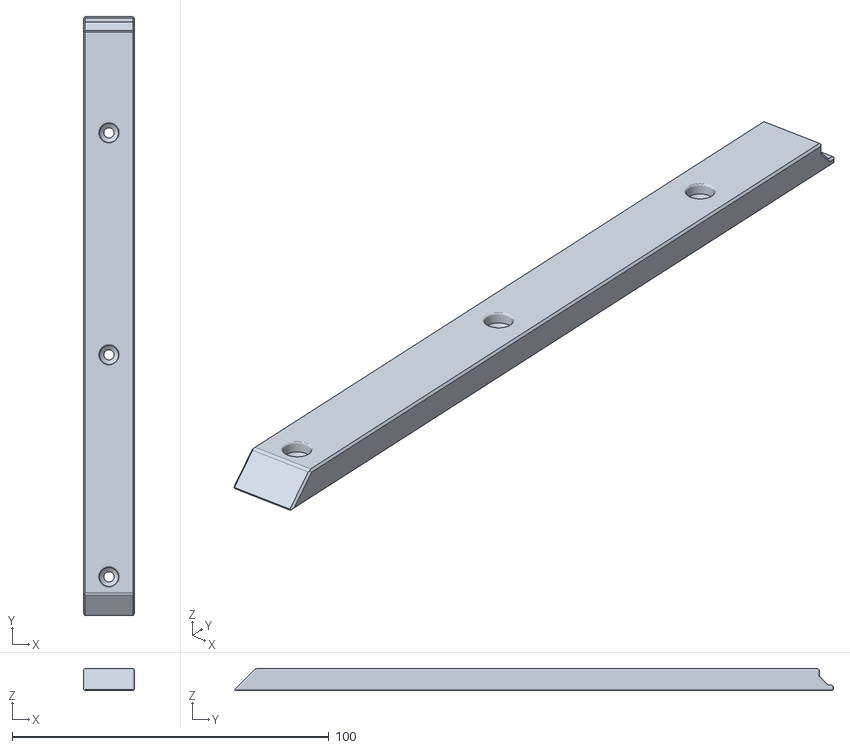
[picture p103: CAD file, 2023-03-23]
STLs/Black/BottomRail_NoRail.stl
16.1 x 189.0 x 7.03
