Sillybutts/Cynthia/STLs/Black/Buttplate_Standard.stl

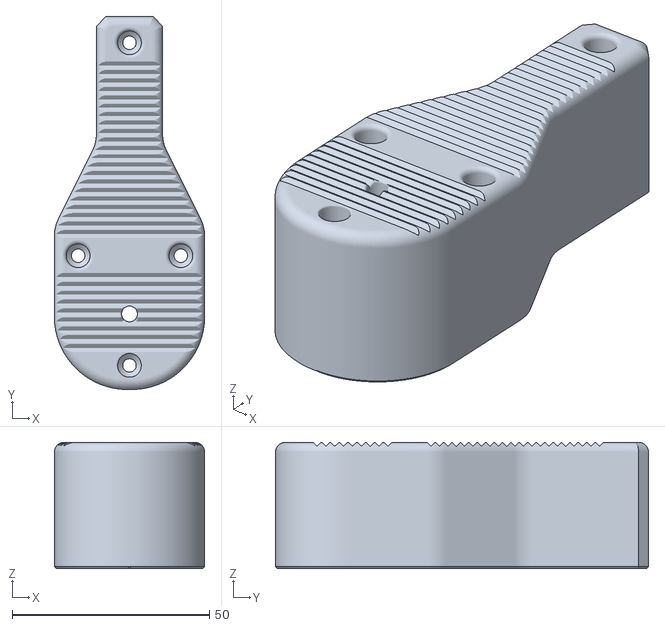
[picture p104: CAD file, 2023-03-23]
STLs/Black/Buttplate_Standard.stl
38.1 x 94.5 x 32.0
